NEhlen/rpi_servo_control_test/src/servo_driver_test.py

import time
from adafruit_servokit import ServoKit
from time import sleep

# Set channels to the number of servo channels on your kit.
# 8 for FeatherWing, 16 for Shield/HAT/Bonnet.
kit = ServoKit(channels=16)

horizontal_min = 45
horizontal_max = 120

vertical_min = 60
vertical_max = 145

kit.servo[0].angle = 45
sleep(0.5)
kit.servo[1].angle = 60
sleep(0.2)

kit.servo[0].angle = None
kit.servo[1].angle = None
